willtmakinen78/FT5/pics/IMG_20210827_170954.jpg

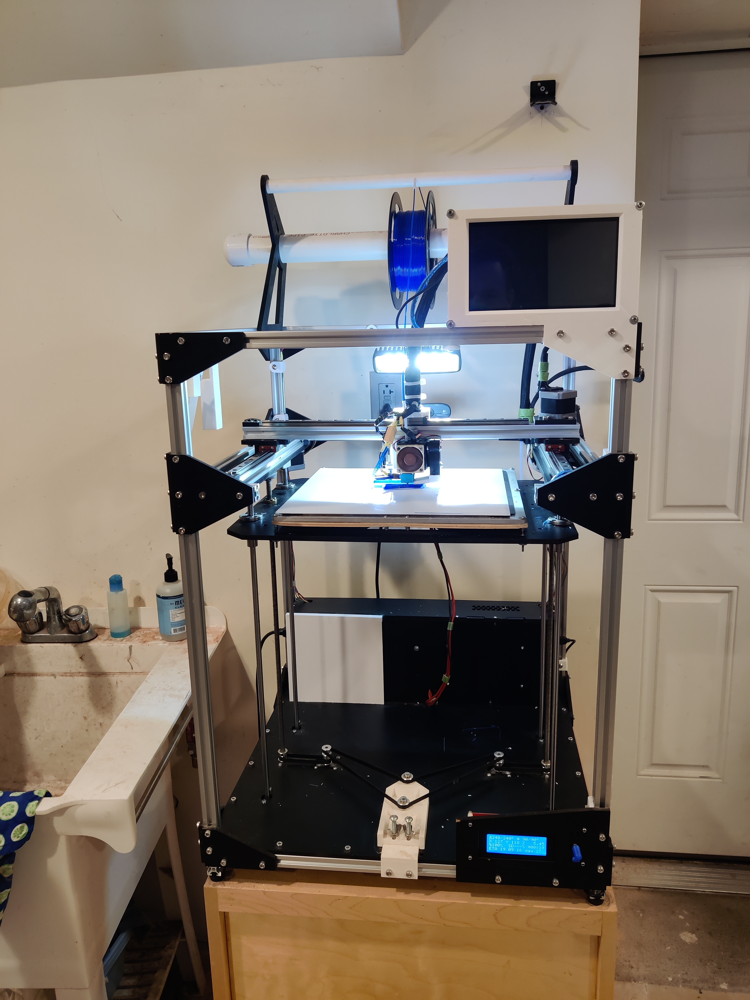
pics/IMG_20210827_170954.jpg
