willtmakinen78/FT5/pics/IMG_20210827_171011.jpg

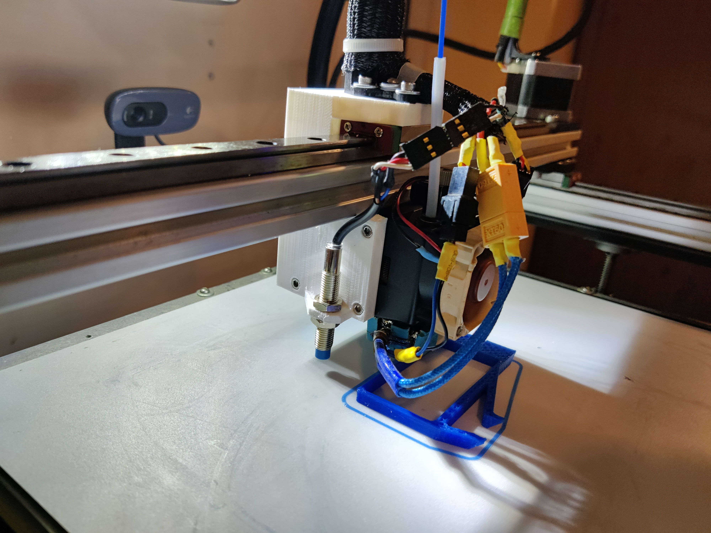
pics/IMG_20210827_171011.jpg
