willtmakinen78/FT5/pics/IMG_20210827_171018.jpg

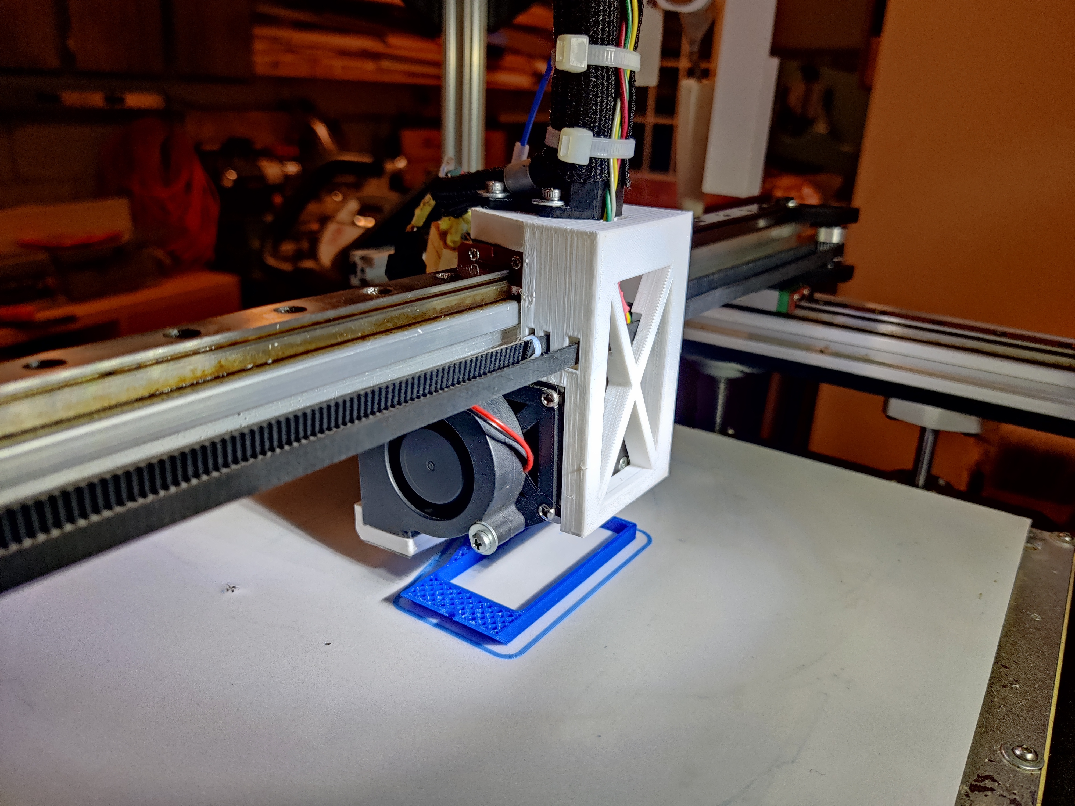
pics/IMG_20210827_171018.jpg
