willtmakinen78/FT5/pics/IMG_20210827_171033.jpg

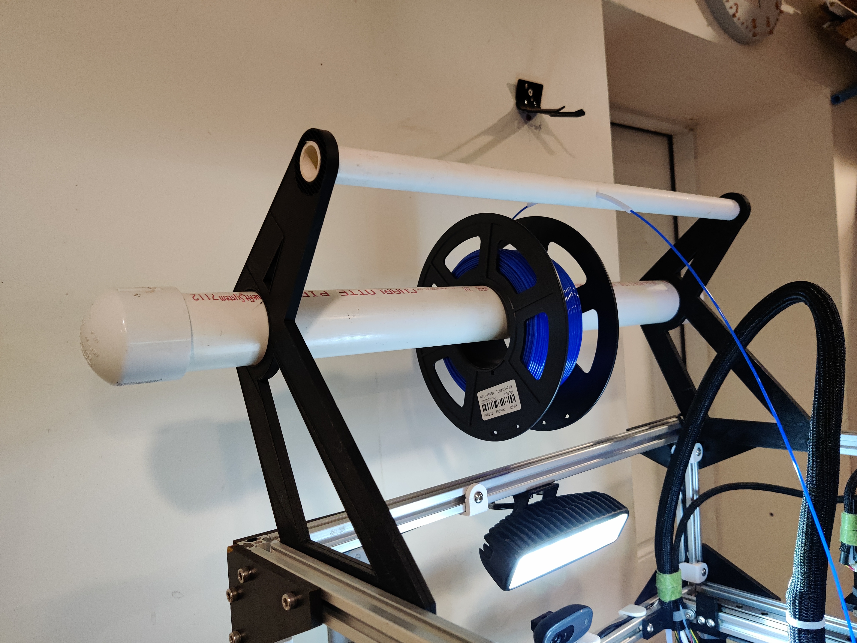
pics/IMG_20210827_171033.jpg
