willtmakinen78/FT5/pics/IMG_20210827_171058.jpg

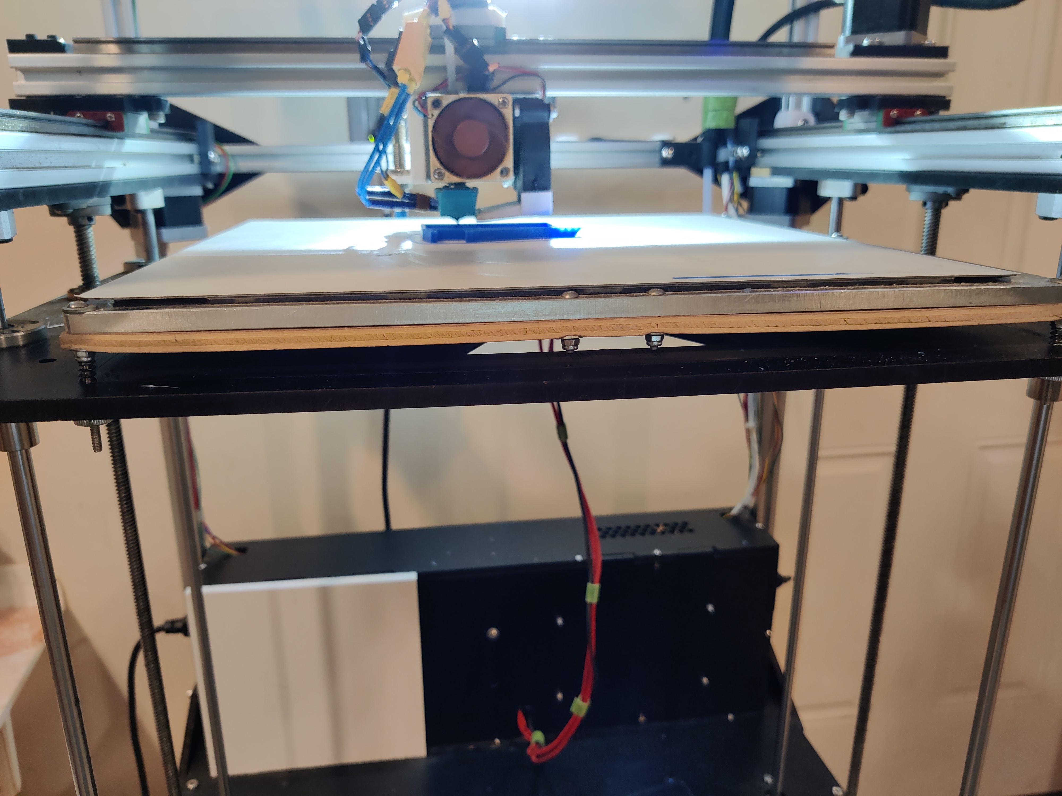
pics/IMG_20210827_171058.jpg
