willtmakinen78/FT5/pics/IMG_20210827_171116.jpg

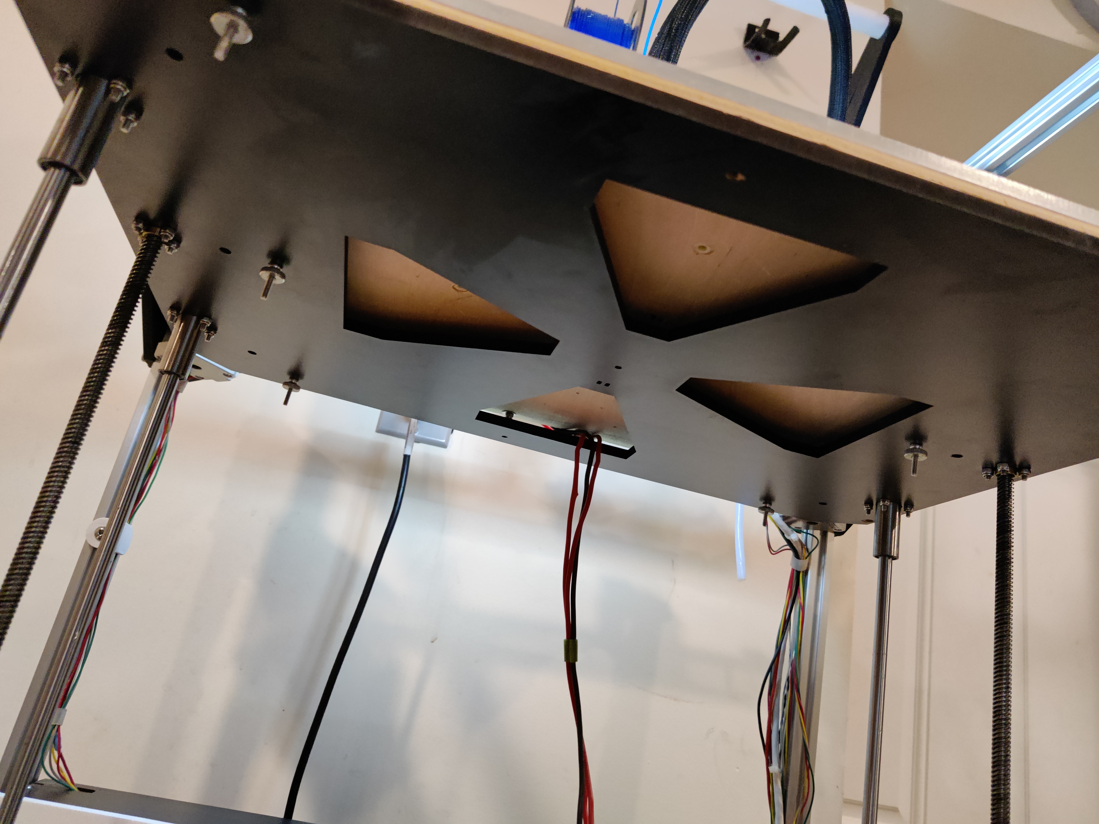
pics/IMG_20210827_171116.jpg
