willtmakinen78/FT5/cad/Hermes_Mount/Hermes_LayerFan_Mount/Hermes_LayerFan_Mount_2.stl

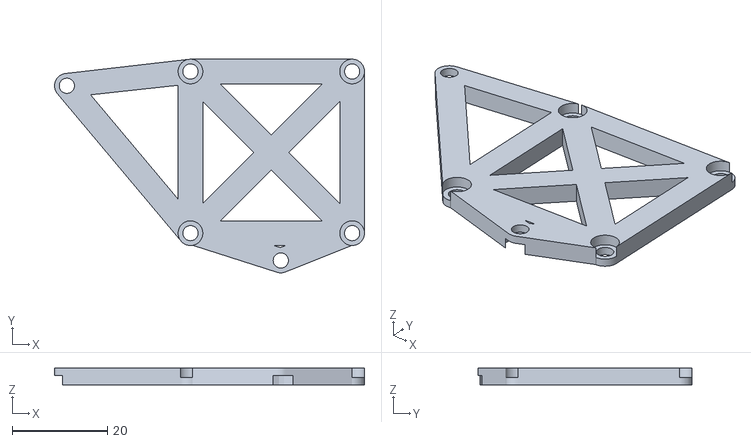
[picture p24: CAD file, 2021-09-04]
cad/Hermes_Mount/Hermes_LayerFan_Mount/Hermes_LayerFan_Mount_2.stl
65.2 x 44.9 x 3.50
