willtmakinen78/FT5/cad/Hermes_Mount/Hermes_Mount_Fan/Hemera_5015_FanDuct_redangel1984_V1.1.1.stl

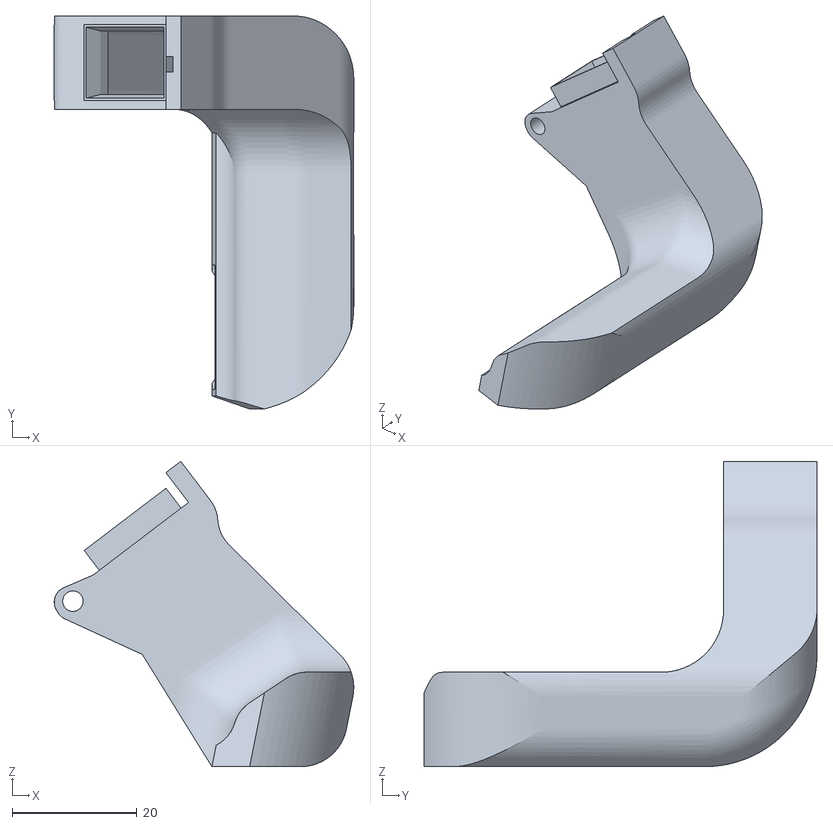
[picture p25: CAD file, 2021-09-04]
cad/Hermes_Mount/Hermes_Mount_Fan/Hemera_5015_FanDuct_redangel1984_V1.1.1.stl
48.1 x 63.1 x 49.0
