willtmakinen78/FT5/cad/Hermes_Mount/Hermes_Mount_Frame/X_Axis_Stopper.stl

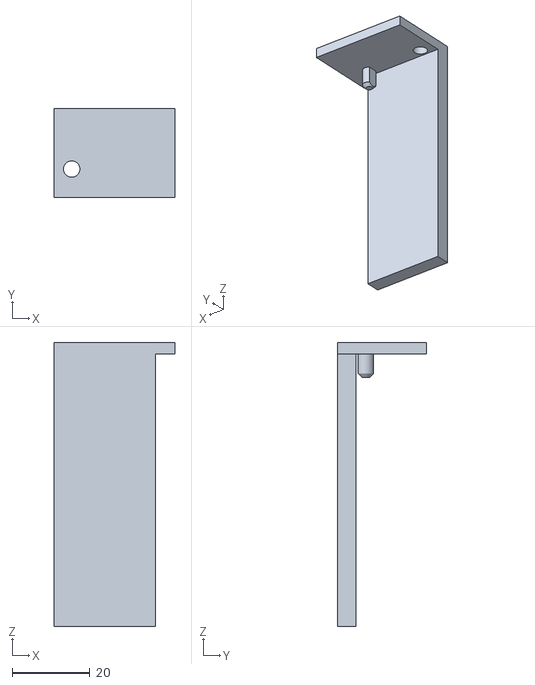
[picture p26: CAD file, 2021-09-04]
cad/Hermes_Mount/Hermes_Mount_Frame/X_Axis_Stopper.stl
31.0 x 22.8 x 73.0
