willtmakinen78/FT5/cad/Roof_Cable_Holder/Loop_X.stl

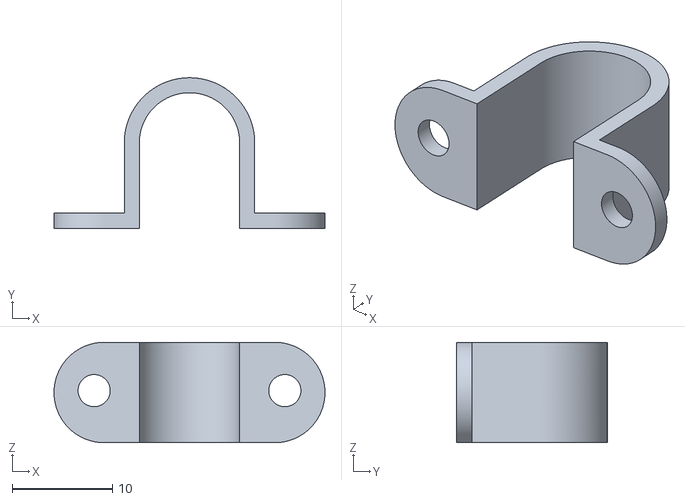
[picture p27: CAD file, 2021-09-04]
cad/Roof_Cable_Holder/Loop_X.stl
27.0 x 15.0 x 10.0
