willtmakinen78/FT5/cad/Webcam_Mount/FT5_Webcam_Mount_R1_1.stl

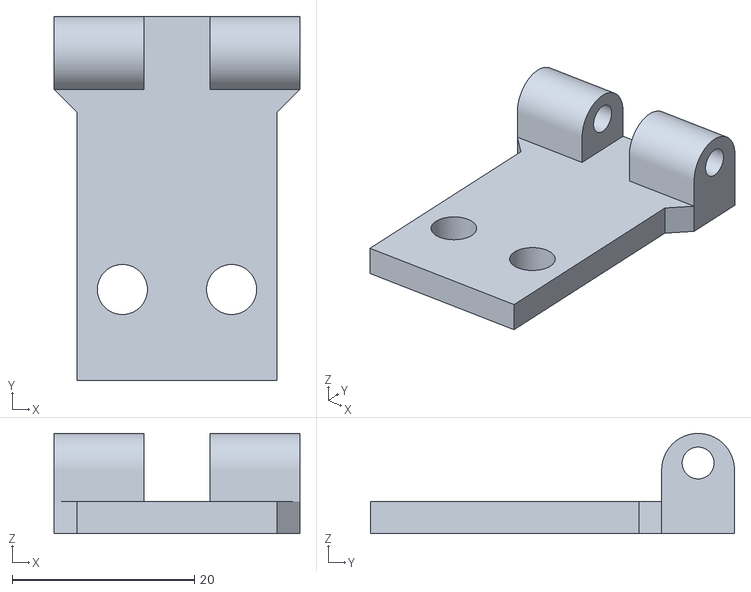
[picture p28: CAD file, 2021-09-04]
cad/Webcam_Mount/FT5_Webcam_Mount_R1_1.stl
27.0 x 40.0 x 11.0
