willtmakinen78/FT5/cad/Filament_Holders/Chassis_Bowden_Holder.stl

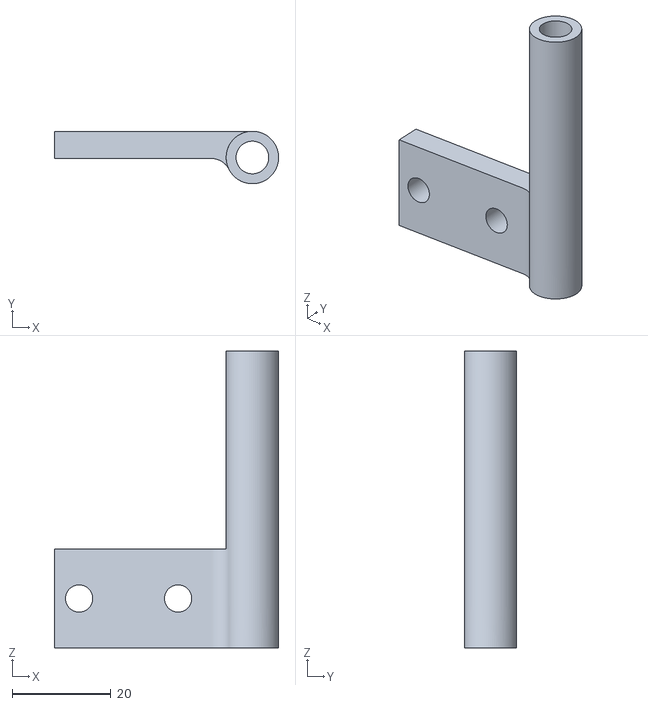
[picture p29: CAD file, 2021-09-04]
cad/Filament_Holders/Chassis_Bowden_Holder.stl
45.3 x 10.6 x 60.0
