willtmakinen78/FT5/cad/FT5_BLTouch_Mount_BMG_Metal_Reinforced/FT5_BLTouch_Mount_BMG_Metal_Reinforced_3.stl

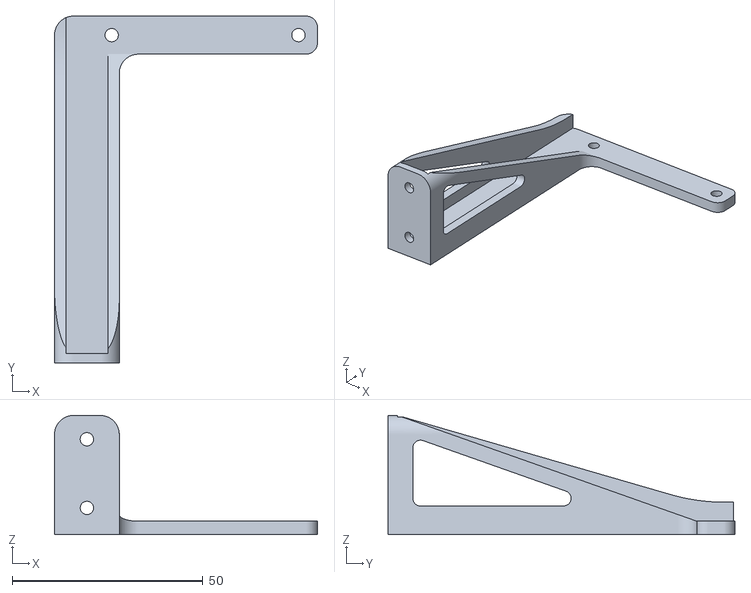
[picture p30: CAD file, 2021-09-04]
cad/FT5_BLTouch_Mount_BMG_Metal_Reinforced/FT5_BLTouch_Mount_BMG_Metal_Reinforced_3.stl
69.0 x 91.0 x 31.2
