willtmakinen78/FT5/cad/Hermes_Mount/Hermes_LayerFan_Mount/Hermes_LayerFan_Shroud_3.stl

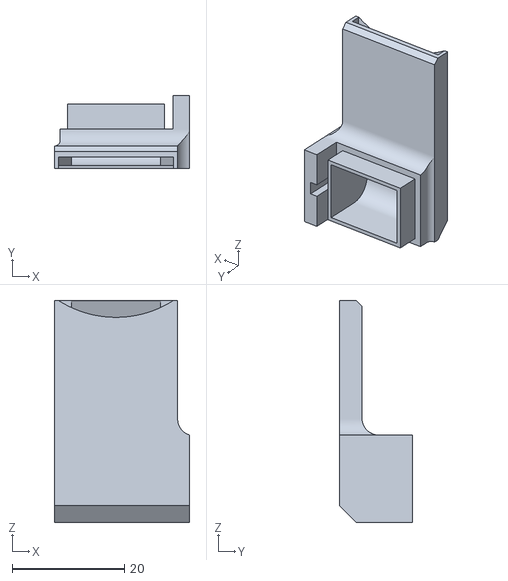
[picture p31: CAD file, 2021-09-04]
cad/Hermes_Mount/Hermes_LayerFan_Mount/Hermes_LayerFan_Shroud_3.stl
24.1 x 13.0 x 39.6
