willtmakinen78/FT5/cad/Roof_Cable_Holder/Loop.stl

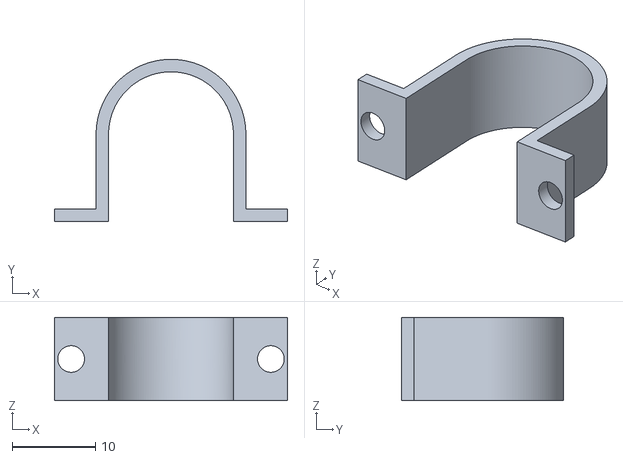
[picture p32: CAD file, 2021-09-04]
cad/Roof_Cable_Holder/Loop.stl
28.0 x 19.5 x 10.0
