willtmakinen78/FT5/cad/TouchScreen_Mount/Raspi7inch_Case_Split.stl

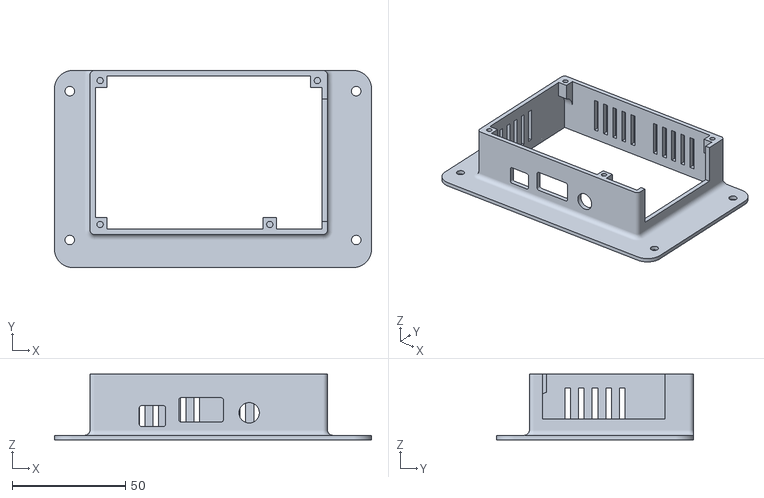
[picture p33: CAD file, 2021-09-04]
cad/TouchScreen_Mount/Raspi7inch_Case_Split.stl
140.0 x 87.0 x 29.0
