willtmakinen78/FT5/cad/Filament_Holders/Extruder_Wire_Holder_R1_3.stl

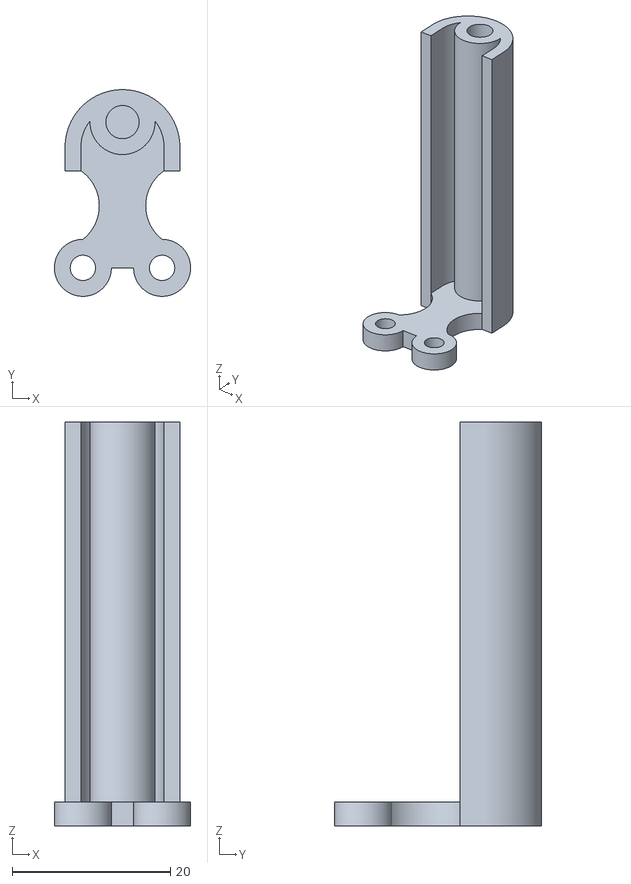
[picture p34: CAD file, 2021-09-04]
cad/Filament_Holders/Extruder_Wire_Holder_R1_3.stl
17.2 x 26.1 x 51.0
