willtmakinen78/FT5/cad/Hermes_Mount/Hermes_LayerFan_Mount/Hermes_LayerFan_Shroud_2.stl

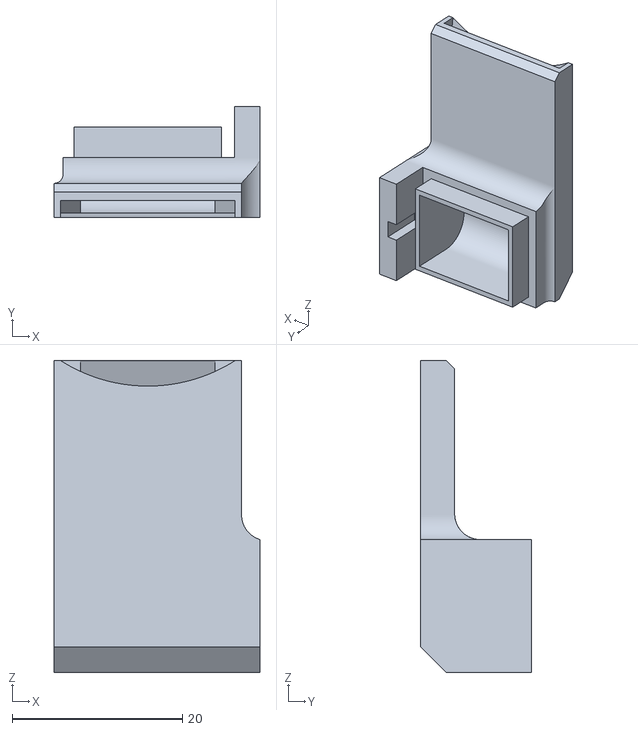
[picture p35: CAD file, 2021-09-04]
cad/Hermes_Mount/Hermes_LayerFan_Mount/Hermes_LayerFan_Shroud_2.stl
24.1 x 13.0 x 36.6
