willtmakinen78/FT5/cad/Hermes_Mount/Hermes_Mount_Frame/Hermes_Mount_R3_2.3mf

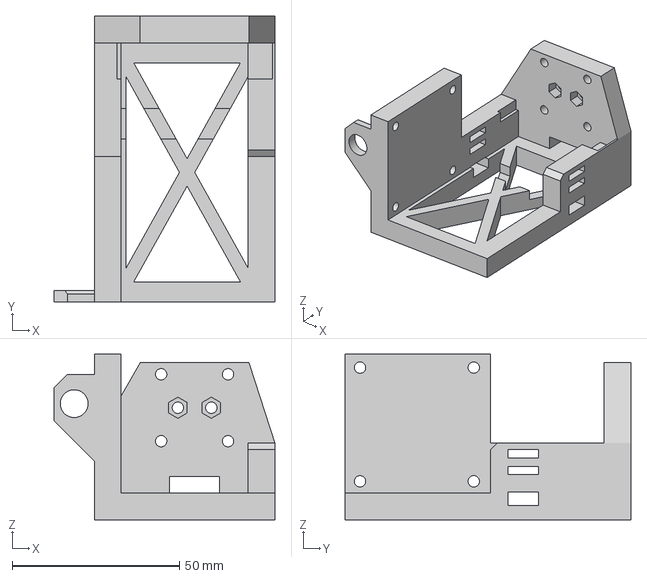
[picture p36: CAD file, 2021-09-04]
cad/Hermes_Mount/Hermes_Mount_Frame/Hermes_Mount_R3_2.3mf
66.0 x 85.5 x 49.5 mm
