willtmakinen78/FT5/cad/Roof_Cable_Holder/Swivel_X.stl

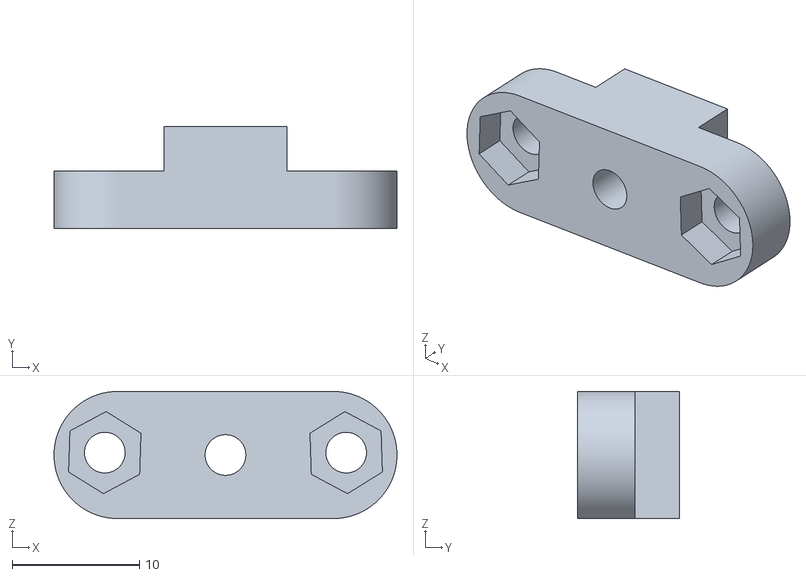
[picture p37: CAD file, 2021-09-04]
cad/Roof_Cable_Holder/Swivel_X.stl
27.0 x 8.00 x 10.0
