willtmakinen78/FT5/cad/TouchScreen_Mount/Printer_Mount_4.stl

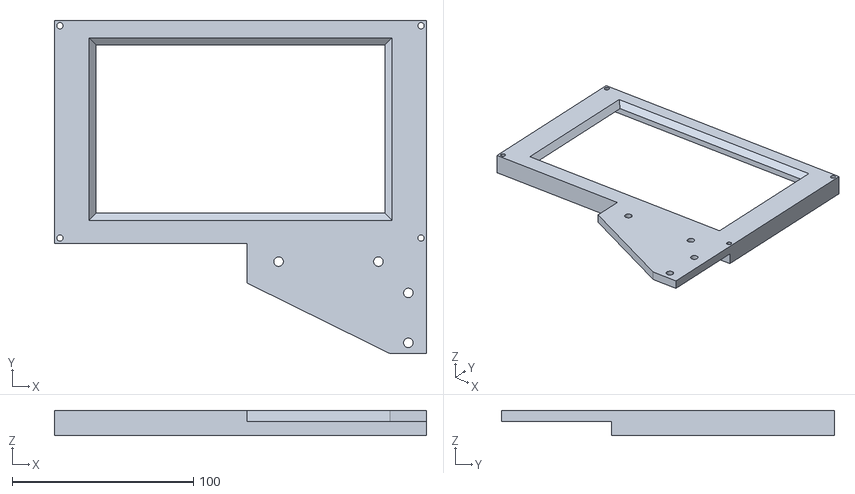
[picture p38: CAD file, 2021-09-04]
cad/TouchScreen_Mount/Printer_Mount_4.stl
205.0 x 183.8 x 13.8
