willtmakinen78/FT5/cad/Filament_Holders/Extruder_Wire_Holder.stl

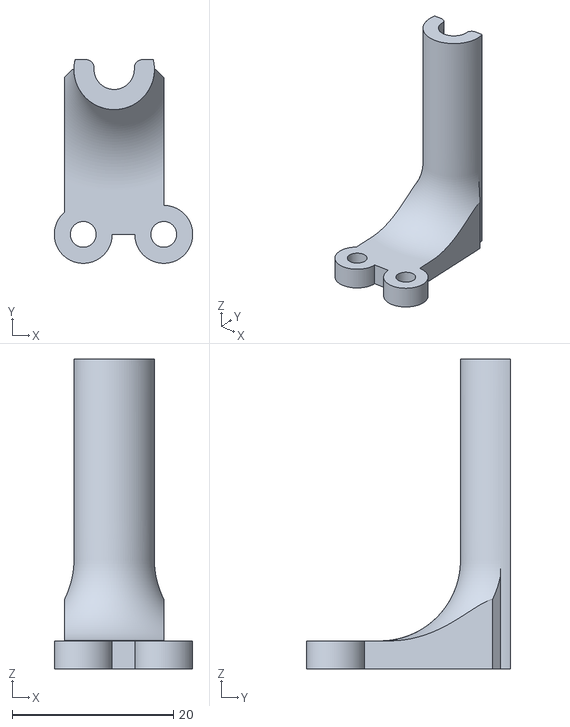
[picture p39: CAD file, 2021-09-04]
cad/Filament_Holders/Extruder_Wire_Holder.stl
17.2 x 25.3 x 38.5
