willtmakinen78/FT5/cad/Hermes_Mount/Hermes_Mount_Frame/Hermes_Mount_R2_2.stl

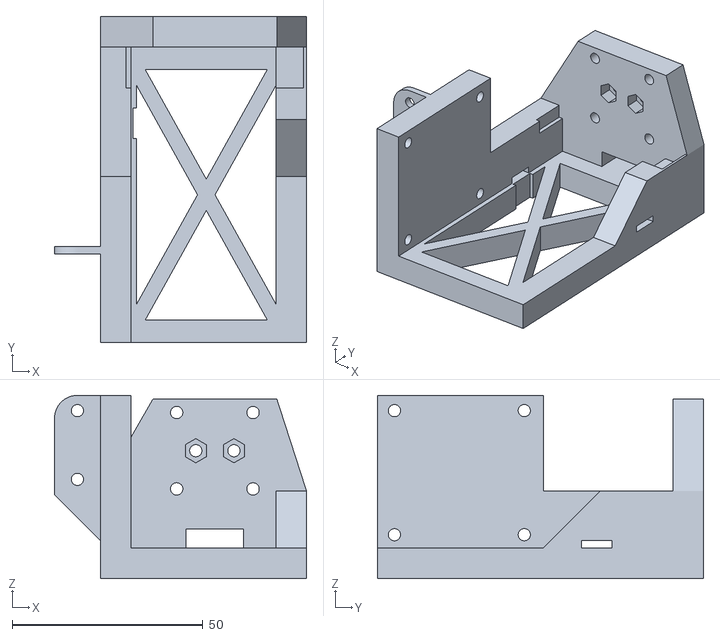
[picture p40: CAD file, 2021-09-04]
cad/Hermes_Mount/Hermes_Mount_Frame/Hermes_Mount_R2_2.stl
66.0 x 85.5 x 48.0
