willtmakinen78/FT5/cad/Roof_Cable_Holder/Swivel_1.stl

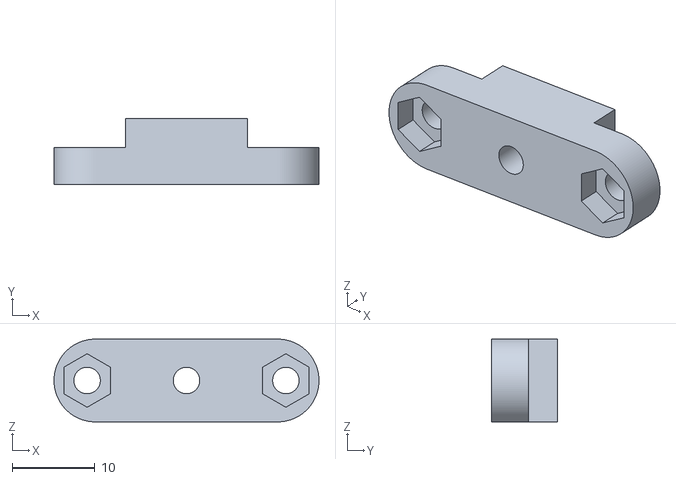
[picture p41: CAD file, 2021-09-04]
cad/Roof_Cable_Holder/Swivel_1.stl
32.0 x 8.00 x 10.0
