willtmakinen78/FT5/cad/TouchScreen_Mount/Printer_Mount_2.stl

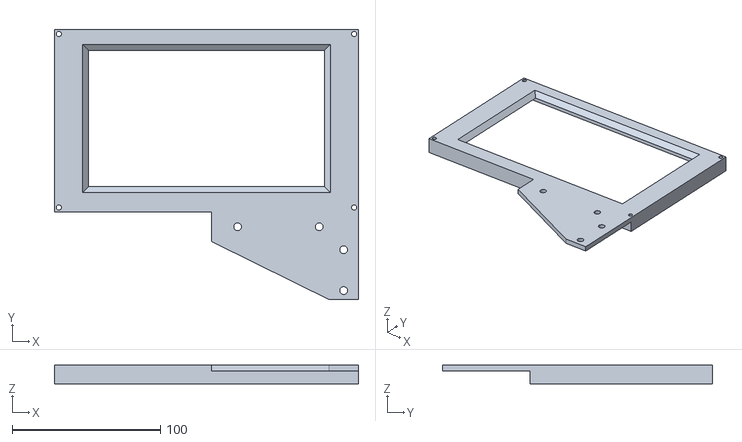
[picture p42: CAD file, 2021-09-04]
cad/TouchScreen_Mount/Printer_Mount_2.stl
205.0 x 182.0 x 12.8
