willtmakinen78/FT5/cad/Filament_Holders/Extruder_Filament_Holder.stl

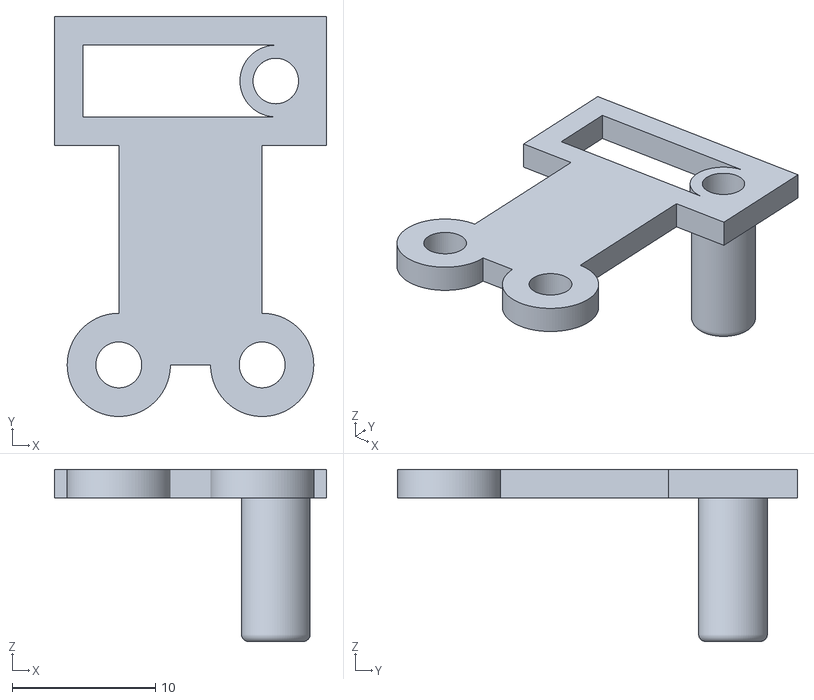
[picture p43: CAD file, 2021-09-04]
cad/Filament_Holders/Extruder_Filament_Holder.stl
19.0 x 27.9 x 12.0
