willtmakinen78/FT5/cad/Hermes_Mount/Hermes_LayerFan_Mount/Hermes_LayerFan_Shroud_1.stl

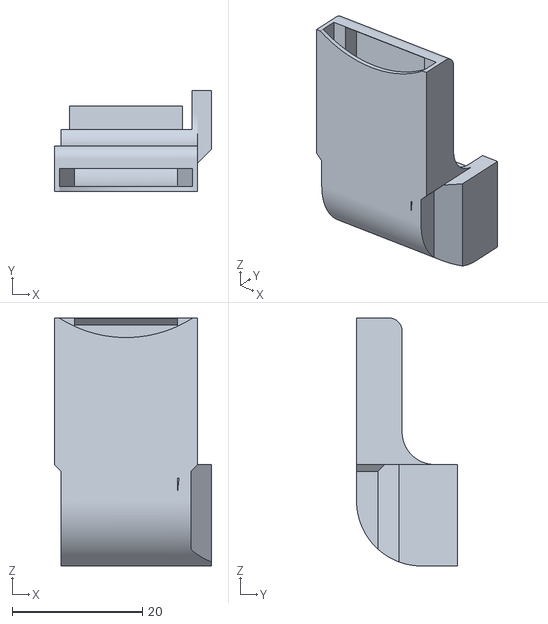
[picture p44: CAD file, 2021-09-04]
cad/Hermes_Mount/Hermes_LayerFan_Mount/Hermes_LayerFan_Shroud_1.stl
24.1 x 15.5 x 38.1
