willtmakinen78/FT5/cad/Hermes_Mount/Hermes_Mount_Frame/Hermes_Mount_Rear.stl

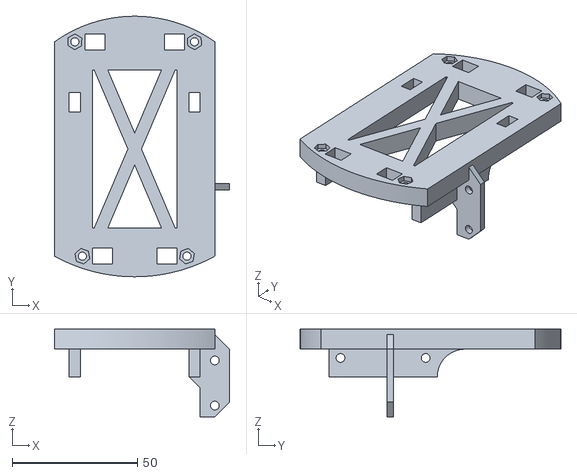
[picture p45: CAD file, 2021-09-04]
cad/Hermes_Mount/Hermes_Mount_Frame/Hermes_Mount_Rear.stl
69.8 x 104.0 x 35.0
