willtmakinen78/FT5/cad/Roof_Cable_Holder/Loop_1.stl

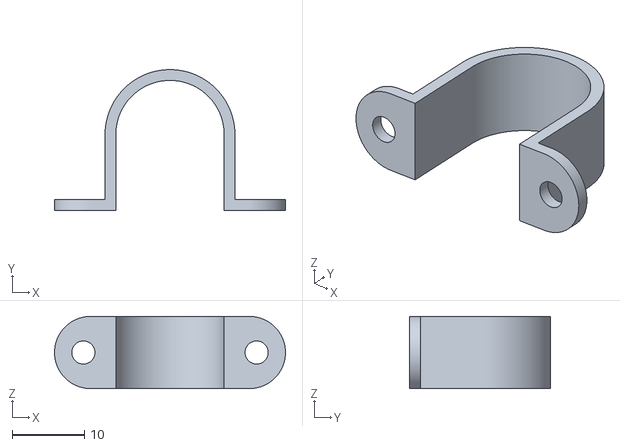
[picture p46: CAD file, 2021-09-04]
cad/Roof_Cable_Holder/Loop_1.stl
32.0 x 19.5 x 10.0
