willtmakinen78/FT5/cad/TouchScreen_Mount/Printer_Mount_1.stl

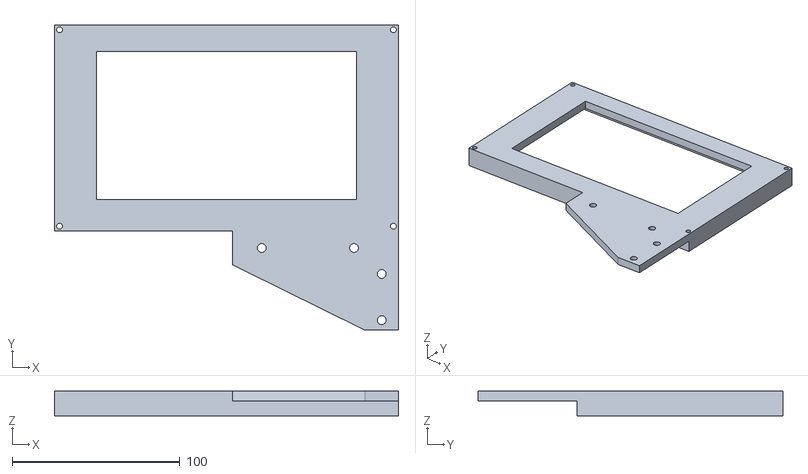
[picture p47: CAD file, 2021-09-04]
cad/TouchScreen_Mount/Printer_Mount_1.stl
205.0 x 182.0 x 14.8
