willtmakinen78/FT5/cad/Filament_Holders/Extruder_Wire_Holder_R2.stl

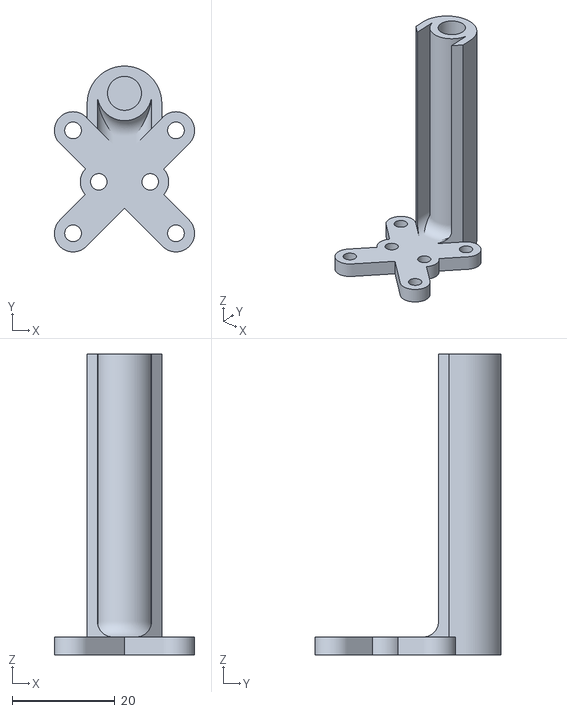
[picture p48: CAD file, 2021-09-04]
cad/Filament_Holders/Extruder_Wire_Holder_R2.stl
27.2 x 36.1 x 58.5
