willtmakinen78/FT5/cad/Hermes_Mount/Hermes_LayerFan_Mount/Hermes_LayerFan_Mount_R1.stl

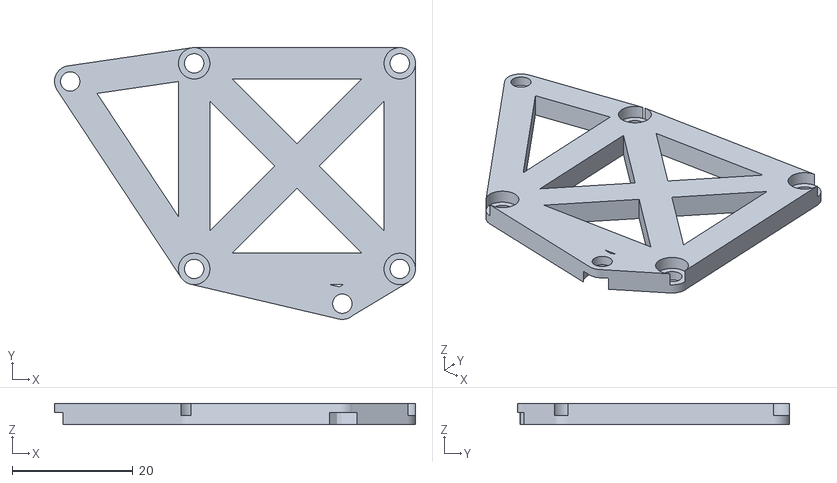
[picture p49: CAD file, 2021-09-04]
cad/Hermes_Mount/Hermes_LayerFan_Mount/Hermes_LayerFan_Mount_R1.stl
59.7 x 44.9 x 3.50
