willtmakinen78/FT5/cad/Filament_Holders/X_Motor_Filament_Holder.stl

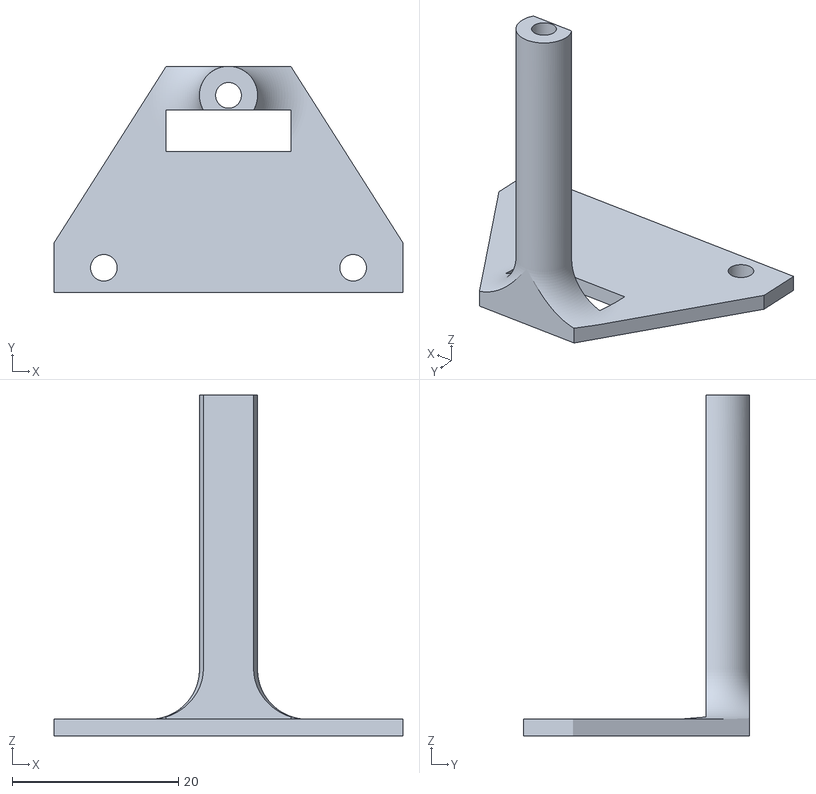
[picture p50: CAD file, 2021-09-04]
cad/Filament_Holders/X_Motor_Filament_Holder.stl
42.0 x 27.2 x 41.0
