willtmakinen78/FT5/cad/Hermes_Mount/Hermes_Mount_Frame/Hermes_Mount_R2.stl

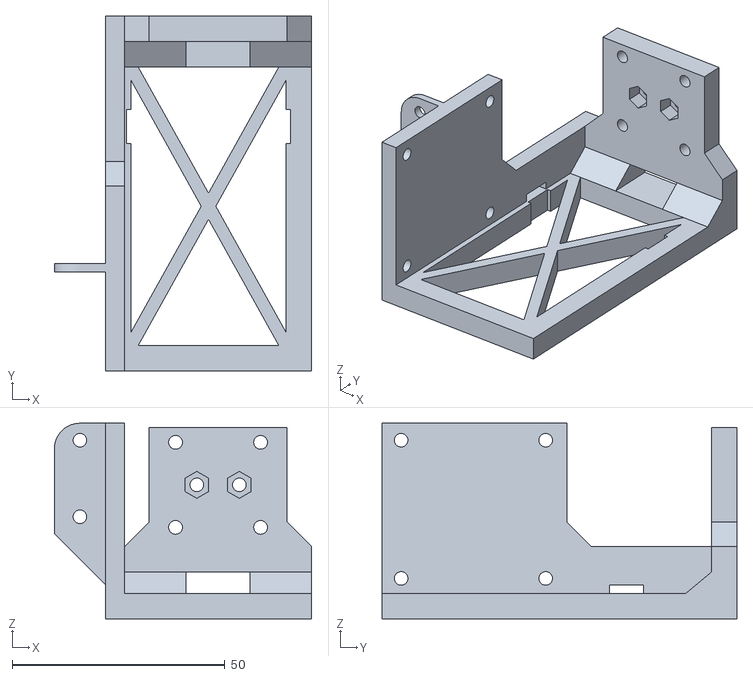
[picture p52: CAD file, 2021-09-04]
cad/Hermes_Mount/Hermes_Mount_Frame/Hermes_Mount_R2.stl
60.5 x 83.5 x 46.0
