willtmakinen78/FT5/cad/TouchScreen_Mount/Printer_Mount_3.stl

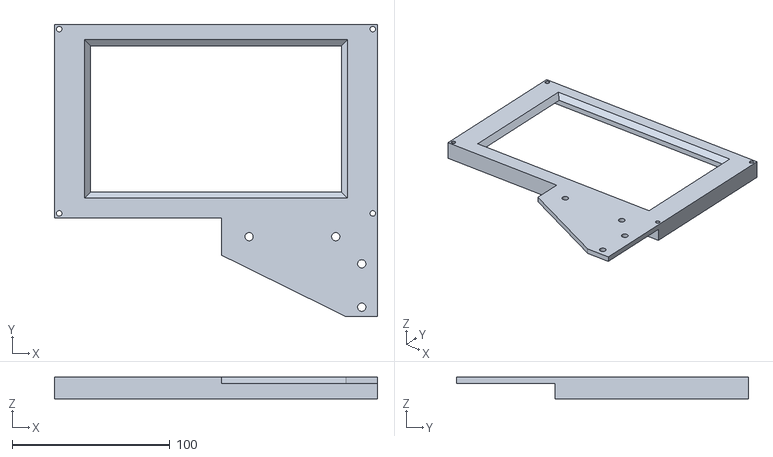
[picture p53: CAD file, 2021-09-04]
cad/TouchScreen_Mount/Printer_Mount_3.stl
205.0 x 185.5 x 13.8
