willtmakinen78/FT5/cad/Filament_Holders/Extruder_Wire_Holder_R1_2.stl

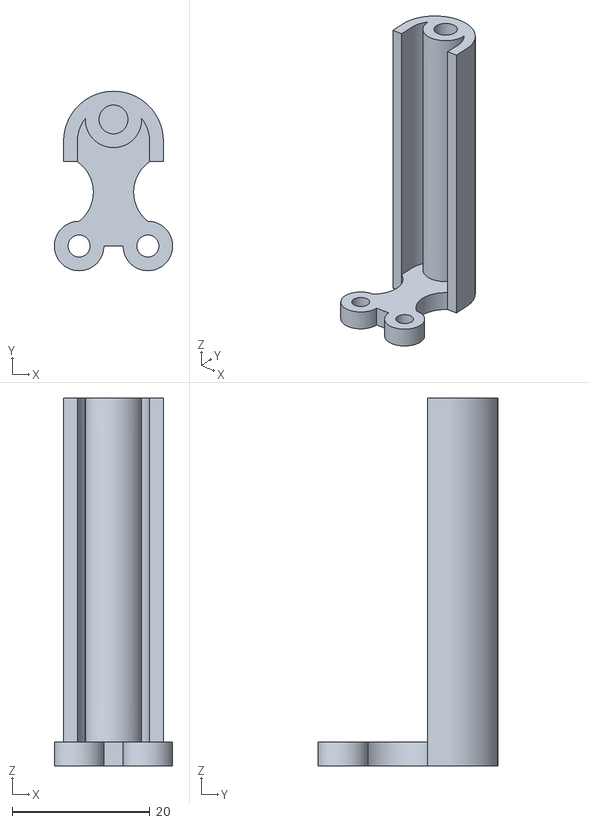
[picture p54: CAD file, 2021-09-04]
cad/Filament_Holders/Extruder_Wire_Holder_R1_2.stl
17.2 x 26.1 x 53.5
