willtmakinen78/FT5/cad/Hermes_Mount/Hermes_Mount_Frame/Hermes_Mount_R1.stl

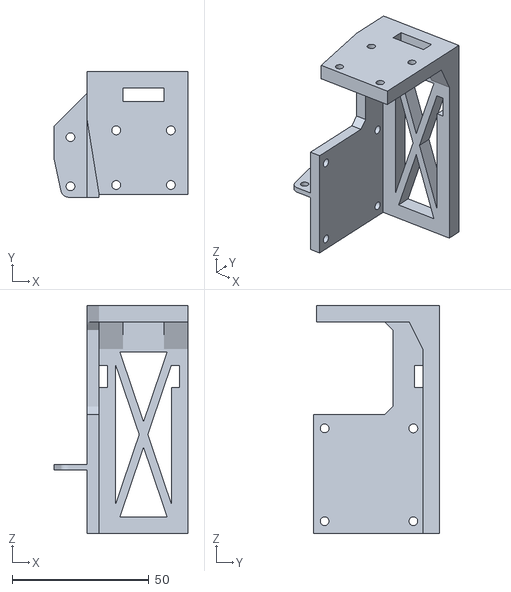
[picture p55: CAD file, 2021-09-04]
cad/Hermes_Mount/Hermes_Mount_Frame/Hermes_Mount_R1.stl
49.0 x 46.0 x 83.5
