willtmakinen78/FT5/cad/TouchScreen_Mount/Raspi7inch_Case.stl

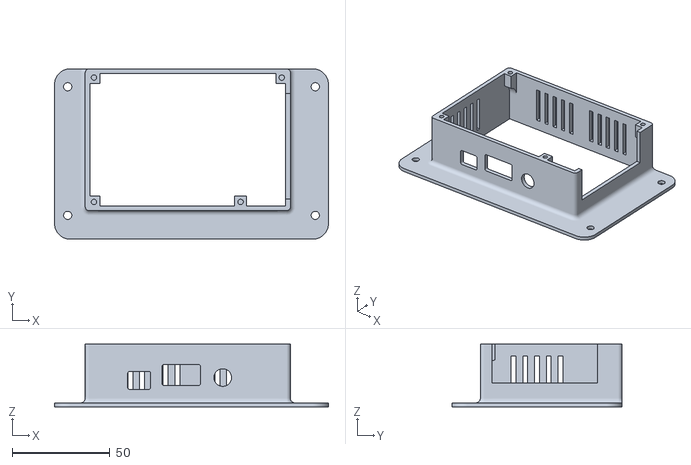
[picture p56: CAD file, 2021-09-04]
cad/TouchScreen_Mount/Raspi7inch_Case.stl
140.0 x 87.0 x 32.0
