willtmakinen78/FT5/cad/TouchScreen_Mount/Back_Plate.stl

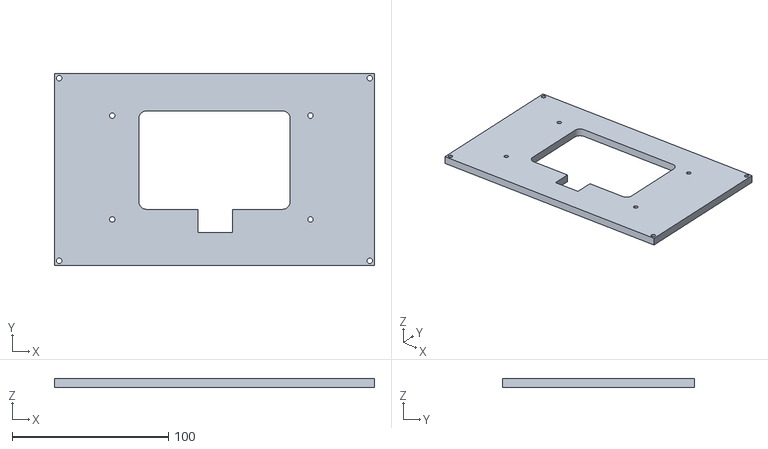
[picture p60: CAD file, 2021-09-04]
cad/TouchScreen_Mount/Back_Plate.stl
205.0 x 123.0 x 6.00
