willtmakinen78/FT5/cad/TouchScreen_Mount/Raspi7inch_Lid.stl

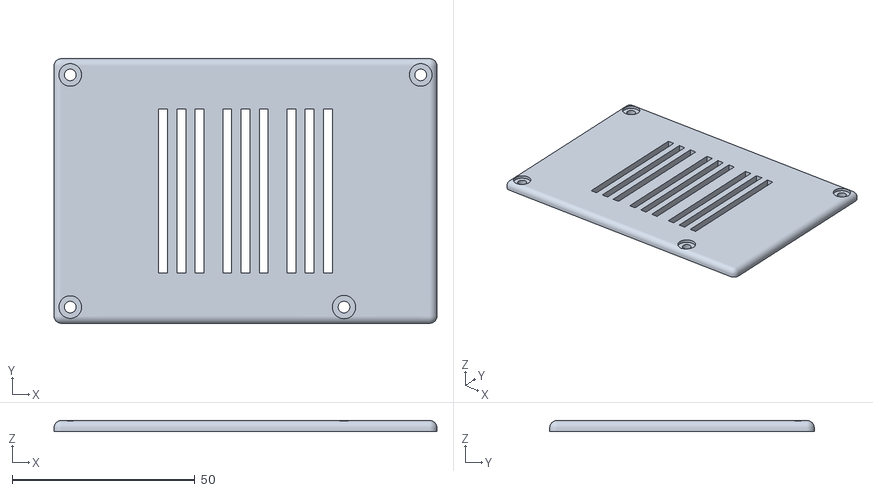
[picture p61: CAD file, 2021-09-04]
cad/TouchScreen_Mount/Raspi7inch_Lid.stl
104.8 x 72.4 x 3.00
