willtmakinen78/FT5/cad/Filament_Holders/Extruder_Wire_Holder_R2_1.stl

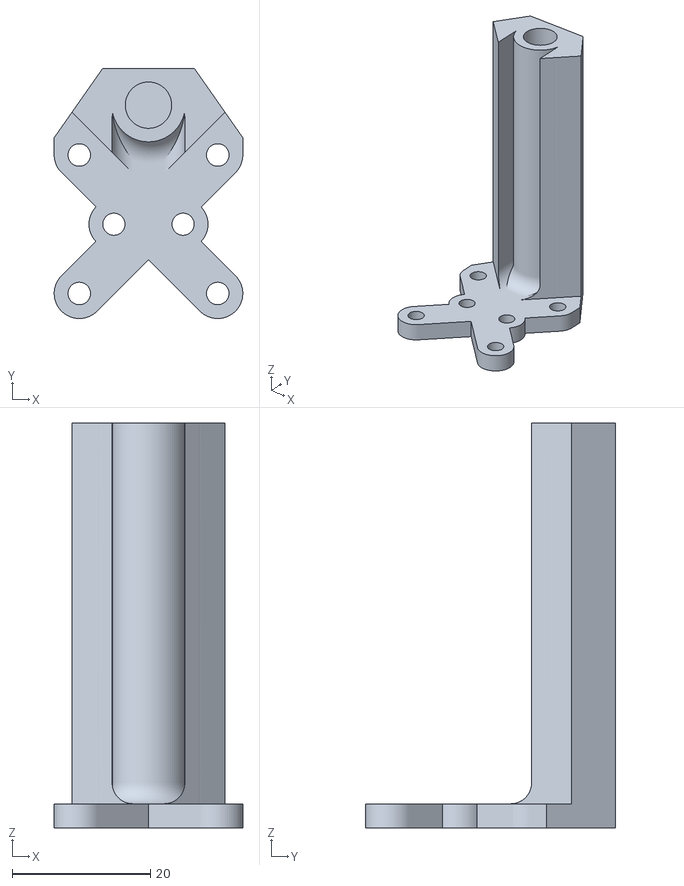
[picture p62: CAD file, 2021-09-04]
cad/Filament_Holders/Extruder_Wire_Holder_R2_1.stl
27.2 x 36.1 x 58.5
