willtmakinen78/FT5/cad/Hermes_Mount/Hermes_Mount_Frame/X_Axis_Stopper_1.stl

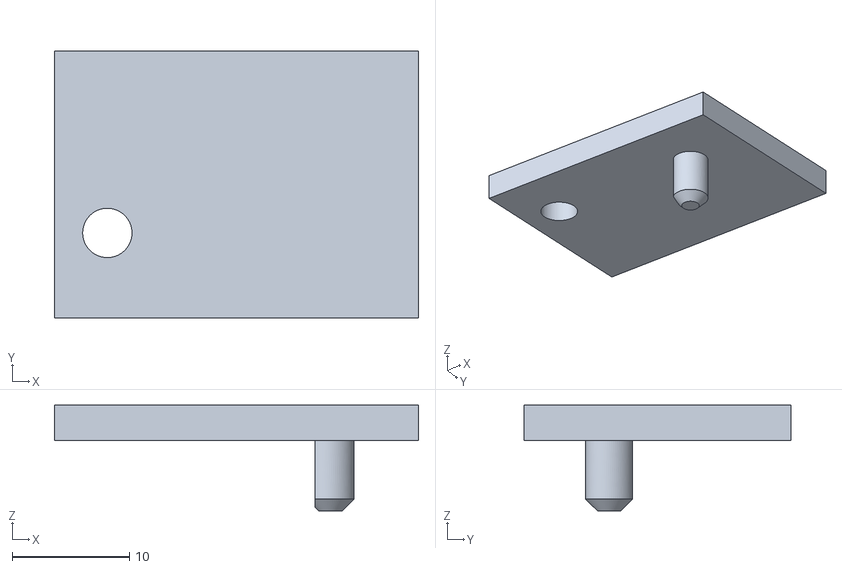
[picture p64: CAD file, 2021-09-04]
cad/Hermes_Mount/Hermes_Mount_Frame/X_Axis_Stopper_1.stl
31.0 x 22.8 x 9.00
