willtmakinen78/FT5/cad/Filament_Holders/Extruder_Filament_Holder_2.stl

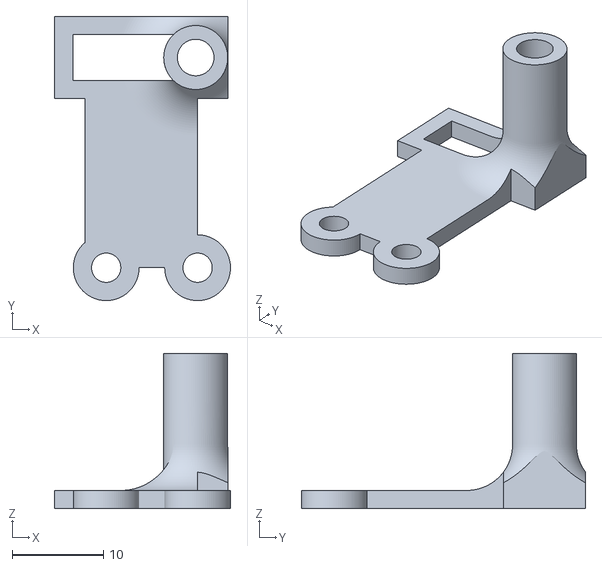
[picture p65: CAD file, 2021-09-04]
cad/Filament_Holders/Extruder_Filament_Holder_2.stl
19.3 x 31.1 x 17.0
