willtmakinen78/FT5/cad/Filament_Holders/X_Motor_Wire_Holder.stl

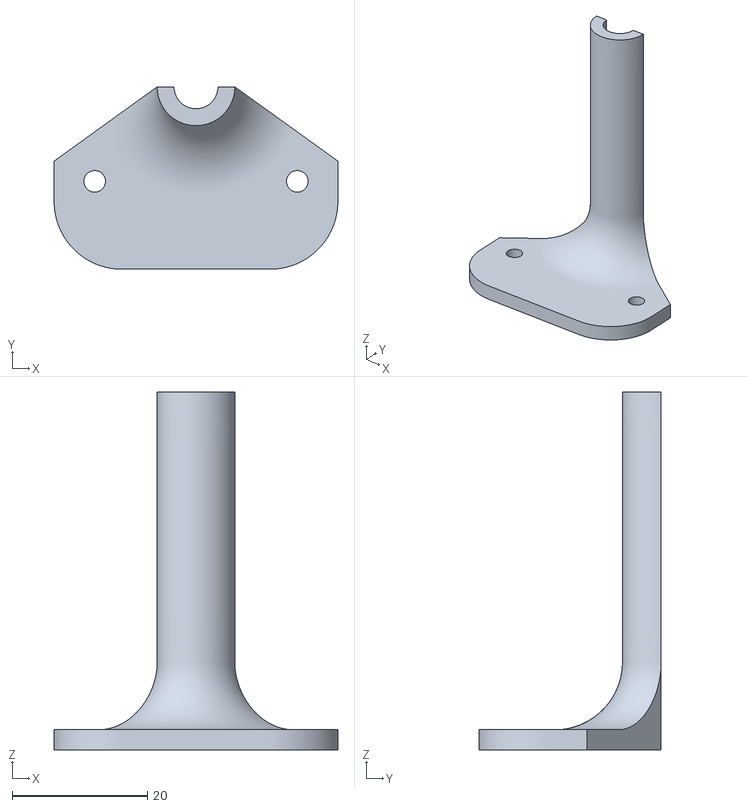
[picture p70: CAD file, 2021-09-04]
cad/Filament_Holders/X_Motor_Wire_Holder.stl
42.0 x 27.0 x 53.0
